kmatzen/millennium/HANDOFF.md

# Millennium continuation handoff

The authoritative objective is to address every unchecked item in
[`TODO.md`](TODO.md). Do not treat a passing QEMU run as proof of a physical
Zero 2 W, radio, USB, audio, power, or first-time-user requirement.

## Current repository state

- Working branch: `main`.
- Current candidate `27b69be9a35c361adab7c90882842096d9612346`
  supersedes and rejects `7033d94` and `c409237`. Physical boot of `c409237`
  proved owner Wi-Fi association, setup-AP shutdown, and the outbound
  maintenance tunnel, but both application and OS update checks failed at
  systemd namespace setup because their persistent state roots were absent.
  `27b69be` provisions every production `ReadWritePaths` state root (`ota`,
  `os-ota`, `hil`, `backup`, and `physical-tests`) with required ownership and
  modes. Exact-image acceptance checks and writes every root through
  `ProtectSystem=strict` on both system slots. The full QEMU lab, host suite,
  contracts suite, and formal release gate passed on `anima`. The canonical
  package is signed with `release-2026-08` and independently verified on
  macOS, `anima`, and external `UEBuild`; dedicated-media write/readback and
  physical boot remain open. Evidence is in
  `hardware/as-built/phone-001/evidence/zero2w-recovery-seeded-artifact-27b69be-2026-09-11.json`.
- Candidate `4a15bf63c9d4a44532d015f8212d44a2a987e7c1` was built and
  factory-seeded on `anima`. Its exact seeded image passed the commit-bound
  automated release gate. Its canonical recovery manifest is signed with the
  verified active `release-2026-08` key and independently verified on macOS
  and `anima`. The non-overwriting external `UEBuild` copy also passed all four
  hashes, signature, public-key identity, and full expansion checks without
  using laptop internal storage. On 2026-09-09 the dedicated 63.9 GB USB card
  was signature-verified, written, flushed, and read back over the complete
  image length; its readback SHA-256 matched the signed expanded digest. The
  card was then safely ejected. Evidence is in
  `hardware/as-built/phone-001/evidence/recovery-media-phone001-4a15bf6.json`.
  It is rejected: physical boot showed `daemon.service` failing with
  `203/EXEC` because `/opt/millennium` was `root:root 0750` and the
  unprivileged service user could not traverse it. The
  expanded image is
  `/data2/millennium-build-4a15bf6/phone001-4a15bf6.img`, is
  15,636,365,312 bytes, and has SHA-256
  `277044c2d3e2332c07aa7849329ba2589a45136d1eb5110812218c12fd75f8ef`.
- Corrected image-layer source `1f637722b3d2403308392e40912da2c5831ec5e7`
  normalizes `/opt` and `/opt/millennium` to `root:root 0755`. Test-harness
  source `ff277828c6bf0b3f7bb6b6a95294e836c53e1c0a` eliminates the echoed-marker
  false positive, tests both system slots, executes the production daemon as
  user `millennium`, and rejects `203/EXEC`. The unchanged application payload
  remains from `4a15bf6`. The corrected 15,636,365,312-byte factory image has
  SHA-256 `aa1b2b0b1d5b312709666db22d6246ae0cfd921ba13cce595a59893ed5142e71`.
  A fresh full QEMU lab passed at `2026-09-09T18:20:21Z`; its result SHA-256 is
  `09d8e2ab11695b2f09bdc0bcbae4d4a2aa7e64bc764649285ded6e8d7cf552ee`.
  The canonical recovery package is signed and independently verified on
  macOS and `anima`. A direct, non-overwriting external `UEBuild` copy passed
  all four stored hashes, signature, public-key identity, and the complete
  expanded stream without using laptop internal storage. On 2026-09-10 the
  OS-identified 63.9 GB removable card was written, flushed, completely read
  back, matched the signed expanded SHA-256, and safely ejected. Physical boot
  remains open.
  Evidence is in `hardware/as-built/phone-001/evidence/zero2w-recovery-seeded-artifact-1f63772-2026-09-09.json`.
- The prior production images were built from earlier sources. The
  physically booted `6f50d12`, `c9b01fb`, `d895b35`, and `98e018a` candidates are
  rejected. Physical
  `d895b35` tracing proved the Zero 2 W AP-to-station transition can exceed
  seven seconds, while its helper stopped retrying after four; `b496081`
  extends the bounded retry window and adds the measured-delay regression.
  The `98e018a` boot then exposed an activated-but-not-beaconing setup AP;
  `6dad08e` forces every setup/recovery start through a down/up cycle.
- The `98e018a` factory-seeded candidate is signed and verified. Its compressed
  SHA-256 is `62dff50153247725982648819caa0d1f2cd9d755a679264dadb89964c46df795`;
  its expanded and readback SHA-256 is
  `d02b6ee091542cc0ee7158a3e46aa4f3078738b545e275933d91b14bd4a759a6`.
  Media evidence is in
  `hardware/as-built/phone-001/evidence/recovery-media-phone001-98e018a.json`.
- The rejected `d895b35` factory-seeded candidate is signed, independently verified,
  retained on `anima`, copied directly to external `UEBuild`, written to the
  dedicated 63.9 GB recovery card, and fully read back. Its compressed SHA-256
  is `d0bba17c794f1980e23a933fea716552f74d2bee8fd103906d1e84235d9c80e7`;
  its expanded and readback SHA-256 is
  `01273e50f108d50f361672b58b9ccfac98340685bede42a61c895dd91b6c23b9`.
- The latest commit-bound QEMU software lab passed at
  `2026-09-09T18:20:21Z`, including both system slots of the exact corrected
  `1f63772` factory image, production-daemon execution as its service user,
  external captive-portal client, OTA origin and failures, maintenance tunnel,
  virtual MCU/peripheral faults, A/B recovery, experiences, and abrupt power.
  Exact evidence is in
  `/data2/millennium-build-1f63772/repo/tools/qemu/state/artifacts/full-20260909T171854Z/`
  on `anima`.
- CI run `34381944039` passed all jobs for test-harness commit `ff27782`; CI run
  `34377452413` passed image-layer commit `1f63772`. The full-test result
  explicitly records that no physical hardware claim was made.
- Latest completed downloadable-experience commits:
  - `f53b54c` — generated package/catalog schemas and compatibility metadata;
  - `d35f4fa` — deterministic schema-2 packages, bounded extraction, exact file
    inventory, compatibility checks, and persistent package anti-rollback;
  - `40c7df7` — deterministic signed catalog creation and local rollout,
    hold/group/withdrawal/denylist eligibility.
- QEMU hardening is in `13b62a6`; the prior full exact-image evidence was
  generated from the production image and passed all 18 artifact hashes.
- The final local software audit on 2026-09-07 passed 151 host unit tests, 6
  web-authorization tests, 2 owner-boundary tests, 50 content/story/security
  tests, 68 tools tests, every simulator scenario, 16 OTA tests, generated
  schema/version checks, and `git diff --check`.
- The 2026-09-07 plugged-media rerun exposed and fixed two QEMU portability
  defects: initramfs `/run` discarded the exact-image udev aliases before
  systemd consumed them, and Linux does not guarantee the numeric
  `/dev/vportNpM` name. The exact-image harness now injects configuration only
  into its disposable overlay, and the portable lab uses the stable
  `/dev/virtio-ports/millennium.mcu` link. The signed-experience lifecycle also
  establishes the same idle handset state required by the production worker.
- At `2026-09-07T19:13:20Z`, FIDO access to `anima` remained healthy but its
  loopback phone listener `127.0.0.1:22022` was absent; do not infer live-phone
  state until the reverse tunnel returns.

Large QEMU and image artifacts intentionally live on `anima` and external
`UEBuild`, not laptop internal storage. The latest complete QEMU evidence is
`/data2/millennium-build-27b69be/repo/tools/qemu/state/artifacts/full-20260911T004411Z/`
on `anima`; its `full-test-result.json` records a pass with exact production
image userspace tested in both system slots and `physical_hardware_claimed: false`.

## Immediate execution order

1. Write/read back, install, and physically test the signed `27b69be`
   recovery package already verified on external `UEBuild`. Do not redeploy
   rejected `7033d94`, `c409237`, `1f63772`, or
   `4a15bf6`.
   Preserve the rejected `6f50d12`,
   `c9b01fb`, `d895b35`, `98e018a`, and `4a15bf6` media/boot evidence without treating any as
   approval. Both Arduino MCUs are required for the physical health gate;
   phone peripherals may be absent only for explicitly scoped platform
   validation.
2. Publish the immutable release objects and signed stable/beta/device-group
   catalogs with `content/publish_catalog.py` after completing the offline
   content/catalog signing ceremony. FIDO-authenticated access to `anima` is
   working through `/opt/homebrew/bin/ssh`; its operator-writable update root is
   `/home/kmatzen/selfhosted/millennium-updates/www`, bind-mounted read-only into
   the `millennium-updates` nginx container.
   `updates.kmatzen.com` is transport, not trust; signatures remain mandatory.
3. When the assembled phone and operator are available, follow
   [`hardware/as-built/phone-001/NEXT_PHYSICAL_SESSION.md`](hardware/as-built/phone-001/NEXT_PHYSICAL_SESSION.md)
   exactly. That single session is intended to close the remaining P0 physical
   Wi-Fi, A/B OS, power-interruption, recovery-media, external-maintenance,
   as-built, and first-time-caller evidence gaps.

## Required verification

For content/catalog changes, run:

```sh
python3 -m unittest content.tests.test_catalogtool \
  content.tests.test_storytool content.tests.test_content_install \
  content.tests.test_experience_agent content.tests.test_publish_catalog
python3 -m unittest discover -s tools/tests -p 'test_*.py'
python3 tools/generate_experience_schemas.py --check
python3 tools/generate_version_metadata.py --check
git diff --check
```

For full appliance changes, run the retained exact image on `anima`:

```sh
/opt/homebrew/bin/ssh anima \
  'docker exec \
    -e MILLENNIUM_QEMU_EXACT_IMAGE=/image/phone001-1f63772.img \
    -e MILLENNIUM_QEMU_EXACT_KERNEL=/workspace/tools/qemu/state/exact-vmlinuz \
    -e MILLENNIUM_QEMU_EXACT_INITRD=/workspace/tools/qemu/state/exact-initrd \
    millennium-qemu-final-1f63772 tools/qemu/qemu.sh full-test'
```

The custom transport initramfs includes FAT, charset, and nftables modules.
Using the older minimal cloud initramfs creates false boot-partition/firewall
failures and is not an equivalent test.

## Completion discipline

Only check off a TODO item when its scoped evidence exists. In particular,
automated captive-portal probes are not physical iOS/Android/macOS/Windows
tests; QEMU power cuts are not measured Zero 2 W power removal; a tunnel from
the home source network is not a genuinely external maintenance session; and a
scripted story traversal is not a first-time-caller playtest. Preserve failed
evidence and never relabel it as passing.
