kmatzen/millennium/docs/COMPATIBILITY.md

# Generated compatibility metadata

Do not edit this file directly. Run `python3 tools/generate_version_metadata.py`.

| Component | Current value |
| --- | ---: |
| Host and MCU software | `0.4.0` |
| OTA manifest schema | `1` |
| OTA release schema | `1` |
| MCU serial protocol | `2` |
| Story source schema | `1` |
| Story runtime schema | `1` |
| Content manifest schema | `1` |
| Downloadable experience package schema | `2` |
| Downloadable experience catalog schema | `1` |

The host release and both MCU roles must report the same software version.
Protocol or schema changes require an explicit compatibility migration; they
must never be inferred from the marketing version alone.
