kmatzen/millennium/content/AUDIO_LIBRARY.md

# Reusable narrative audio and interaction patterns

The initial reviewed library is embodied by *The House at the End of the Line* 2.1.0. Its clips
are deliberately small, handset-normalized, transcript-backed patterns that a
new story may copy and re-record without inheriting story logic:

| Pattern | Reference clip | Interaction contract |
| --- | --- | --- |
| Invitation | `invitation.wav` | Name the physical action that begins. |
| Choice | `decision.wav` | Speak every valid key and the repeat key. |
| Retry | `decision_retry.wav` | Shorten the prompt without removing choices. |
| Accepted choice | `choose_leave.wav` | Confirm input before any delay. |
| Connection | `dialing.wav` | Explain both online and timeout outcomes. |
| Optional discovery | `coin_secret.wav` | Reward hardware play and state how to return. |
| Interruption | `interrupted.wav` | Reassure the caller and name the resume action. |
| Ending | `leave_result.wav` | State consequence and invite a return. |
| Return recognition | `return_leave.wav` | Acknowledge anonymous persistent state. |
| Coda | `leave_coda.wav` | Pay off the earlier choice without new setup. |
| Incoming callback | physical ring | Respect quiet hours and require an answered handset. |
| Waiting voicemail | `missed.wav` | Preserve a missed return call without nagging. |
| Consequence voicemail | `answer_coda.wav` | Reflect the caller's earlier decision. |

All reference WAVs are mono, 8 kHz, signed 16-bit PCM at -20 LUFS. The source
transcripts and deterministic regeneration command live in
`stories/last_line/regenerate_audio.sh`. New library entries require a
transcript, source/voice and license note, loudness/rate metadata, a VFD-only
fallback, and a scenario that exercises the associated interaction.

These are patterns, not mandatory prose. Authors should preserve the contract
while changing voice, language, and tone to suit the story bible and audience.
