kmatzen/millennium/host/millennium_sdk.h

#ifndef MILLENNIUM_SDK_H
#define MILLENNIUM_SDK_H

#include <stddef.h>
#include <string.h>   /* strlen, for millennium_display_payload_len */
#include <stdint.h>
#include <time.h>
#include "mcu_protocol.h"

#define MCU_COMMAND_QUEUE_CAPACITY 8

/* Forward declarations */
struct millennium_client;
struct millennium_logger;

/* Logger level enumeration */
typedef enum {
    LOGGER_VERBOSE = 0,
    LOGGER_DEBUG,
    LOGGER_INFO,
    LOGGER_WARN,
    LOGGER_ERROR
} logger_level_t;

/* Logger structure */
typedef struct millennium_logger {
    logger_level_t current_level;
} millennium_logger_t;

/* Millennium client structure */
typedef struct millennium_client {
    int display_fd;
    int is_open;
    char *input_buffer;
    size_t input_buffer_size;
    size_t input_buffer_capacity;
    
    /* Event queue - simple linked list implementation */
    struct event_queue_node {
        void *event;
        struct event_queue_node *next;
    } *event_queue_head, *event_queue_tail;
    
    /* Thread handle - using pthread for C89 compatibility */
    void *thread_handle;
    
    char *display_message;
    int display_dirty;
    struct timespec last_update_time;
    void *ua; /* struct ua * */
    
    /* Function pointers for event handling */
    void (*create_and_queue_event_char)(struct millennium_client *client, char event_type, const char *payload);
    void (*create_and_queue_event_ptr)(struct millennium_client *client, void *event);

    /* Serial health tracking */
    struct timespec last_serial_activity;
    struct timespec last_alpha_activity;
    int serial_healthy;
    int reconnect_attempts;
    struct timespec next_reconnect_time;
    char serial_device_path[256];
    int serial_baud_rate;

    /* (#239) Last coin-gate command sent to the validator, replayed after a
     * serial reconnect.  0 until the daemon gates the validator once. */
    uint8_t coin_gate_cmd;

    /* Version-2 framed MCU transport. Critical commands remain pending until
     * the display MCU acknowledges their sequence number. */
    mcu_decoder_t mcu_decoder;
    mcu_replay_guard_t mcu_event_replay;
    uint8_t mcu_tx_sequence;
    uint8_t mcu_protocol_ready;
    struct timespec mcu_protocol_started_at;
    struct timespec mcu_protocol_last_hello_at;
    int serial_replay_pending;
    uint8_t pending_frame[MCU_PROTOCOL_MAX_FRAME];
    size_t pending_frame_length;
    uint8_t pending_sequence;
    int pending_retries;
    struct timespec pending_sent_at;
    uint8_t queued_frames[MCU_COMMAND_QUEUE_CAPACITY][MCU_PROTOCOL_MAX_FRAME];
    size_t queued_frame_lengths[MCU_COMMAND_QUEUE_CAPACITY];
    uint8_t queued_frame_sequences[MCU_COMMAND_QUEUE_CAPACITY];
    size_t command_queue_head;
    size_t command_queue_count;
} millennium_client_t;

/* Function declarations */

/* Logger functions */
logger_level_t millennium_logger_parse_level(const char *level_str);
void millennium_logger_set_level(logger_level_t level);
void millennium_logger_log(logger_level_t level, const char *message);
logger_level_t millennium_logger_get_current_level(void);

/* Millennium client functions */
struct millennium_client *millennium_client_create(void);
void millennium_client_destroy(struct millennium_client *client);
void millennium_client_close(struct millennium_client *client);

/* Event handling */
void millennium_client_create_and_queue_event_char(struct millennium_client *client, char event_type, const char *payload);
void millennium_client_create_and_queue_event_ptr(struct millennium_client *client, void *event);

/* Display and communication */
void millennium_client_set_display(struct millennium_client *client, const char *message);
void millennium_client_write_to_coin_validator(struct millennium_client *client, uint8_t data);
void millennium_client_update(struct millennium_client *client);
void *millennium_client_next_event(struct millennium_client *client);

/* Call functions */
void millennium_client_call(struct millennium_client *client, const char *number);
void millennium_client_answer_call(struct millennium_client *client);
void millennium_client_hangup(struct millennium_client *client);
int millennium_client_send_dtmf(struct millennium_client *client, char key);
void millennium_client_set_ua(struct millennium_client *client, void *ua);

/* Internal functions */
void millennium_client_write_command(struct millennium_client *client, uint8_t command, const uint8_t *data, size_t data_size);
void millennium_client_process_event_buffer(struct millennium_client *client);
char *millennium_client_extract_payload(struct millennium_client *client, char event_type, size_t event_start);
void millennium_client_write_to_display(struct millennium_client *client, const char *message);

/* Serial health and reconnection */
int millennium_client_serial_is_healthy(struct millennium_client *client);
long millennium_client_alpha_idle_seconds(struct millennium_client *client);
void millennium_client_check_serial(struct millennium_client *client);
void millennium_client_serial_activity(struct millennium_client *client);

/* Utility functions */
void list_audio_devices(void);

/* SIP registration status (0=unknown, 1=registered, -1=failed). last_error may be NULL. */
void millennium_sdk_get_sip_status(int *registered, char *last_error, size_t last_error_size);

/* Constants */
#define BAUD_RATE B9600
#define ASYNC_WORKERS 4
#define SERIAL_WATCHDOG_SECONDS 60
#define SERIAL_MAX_BACKOFF_SECONDS 60
#define SERIAL_WATCHDOG_ENABLED 1

/* Largest display payload the protocol-v2 display frame can carry.
 *
 * MUST match `byte buf[100]` in Arduino/sketches/display/display.ino, which
 * rejects any frame declaring more than that (`num_bytes > sizeof(buf)`).
 * The length is also carried in a single byte, so it could never exceed 255
 * regardless.
 *
 * Length and CRC cover exactly this body and the receiver resynchronizes at SOF. */
#define DISPLAY_MAX_PAYLOAD 100

/* Number of bytes millennium_client_write_to_display will actually send for
 * `message`: strlen clamped to DISPLAY_MAX_PAYLOAD, and 0 for NULL.
 *
 * Defined here rather than in millennium_sdk.c so the unit tests can exercise
 * it -- unit_tests does not link millennium_sdk.o, which would pull in the
 * PJSIP symbols that are only available on the Pi.
 *
 * `static inline` (a GNU extension the build already relies on via -std=gnu89)
 * so translation units that never call it do not trip -Wunused-function. */
static inline size_t millennium_display_payload_len(const char *message) {
    size_t len;
    if (!message) return 0;
    len = strlen(message);
    return (len > DISPLAY_MAX_PAYLOAD) ? (size_t)DISPLAY_MAX_PAYLOAD : len;
}

#endif /* MILLENNIUM_SDK_H */
