kmatzen/millennium/host/events.c

#define _POSIX_C_SOURCE 200112L
#include "events.h"
#include "logger.h"
#include <stdlib.h>
#include <string.h>
#include <stdio.h>

size_t event_payload_length(char event_type) {
    switch (event_type) {
    case EVENT_TYPE_KEYPAD:
    case EVENT_TYPE_HOOK:
    case EVENT_TYPE_COIN:
        return 1;
    case EVENT_TYPE_CARD:
        return 16;
    case EVENT_TYPE_EEPROM_ERROR:
        return 3;
    case EVENT_TYPE_DIAG:
        return EVENT_DIAG_PAYLOAD_LEN;
    default:
        return 0;
    }
}

/* Helper function to create a string copy */
static char *strdup_safe(const char *src) {
    size_t len;
    char *dst;
    if (!src) return NULL;
    len = strlen(src);
    dst = malloc(len + 1);
    if (dst) {
        memcpy(dst, src, len);
        dst[len] = '\0';
    }
    return dst;
}

/* Keypad event functions */
static void keypad_event_destroy(void *event) {
    free(event);
}

static const char *keypad_event_get_name(void *event) {
    (void)event;
    return "KeypadEvent";
}

static char *keypad_event_get_repr(void *event) {
    keypad_event_t *ke = (keypad_event_t *)event;
    char *repr = malloc(2);
    if (repr) {
        repr[0] = ke->key;
        repr[1] = '\0';
    }
    return repr;
}

keypad_event_t *keypad_event_create(char key) {
    keypad_event_t *event = malloc(sizeof(keypad_event_t));
    if (!event) return NULL;
    
    event->base.type = EVENT_KEYPAD;
    event->base.destroy = keypad_event_destroy;
    event->base.get_name = keypad_event_get_name;
    event->base.get_repr = keypad_event_get_repr;
    event->key = key;
    
    return event;
}

char keypad_event_get_key(keypad_event_t *event) {
    return event ? event->key : 0;
}

/* Card event functions */
static void card_event_destroy(void *event) {
    card_event_t *card = (card_event_t *)event;
    if (card) memset(card->card_number, 0, sizeof(card->card_number));
    free(event);
}

static const char *card_event_get_name(void *event) {
    (void)event;
    return "CardEvent";
}

static char *card_event_get_repr(void *event) {
    (void)event;
    return strdup_safe("[credential redacted]");
}

card_event_t *card_event_create(const char *card_number) {
    card_event_t *event = malloc(sizeof(card_event_t));
    if (!event) return NULL;
    
    event->base.type = EVENT_CARD;
    event->base.destroy = card_event_destroy;
    event->base.get_name = card_event_get_name;
    event->base.get_repr = card_event_get_repr;
    
    if (card_number) {
        strncpy(event->card_number, card_number, sizeof(event->card_number) - 1);
        event->card_number[sizeof(event->card_number) - 1] = '\0';
    } else {
        event->card_number[0] = '\0';
    }
    
    return event;
}

/* Coin event functions */
static void coin_event_destroy(void *event) {
    free(event);
}

static const char *coin_event_get_name(void *event) {
    (void)event;
    return "CoinEvent";
}

static char *coin_event_get_repr(void *event) {
    return coin_event_get_coin_code((coin_event_t *)event);
}

char *coin_event_get_coin_code(coin_event_t *event) {
    if (!event) return NULL;
    
    switch (event->code) {
    case 0x30:
        return strdup_safe("INVALID_COIN");
    case 0x31:
        return strdup_safe("COIN_1");
    case 0x32:
        return strdup_safe("COIN_2");
    case 0x33:
        return strdup_safe("COIN_3");
    case 0x34:
        return strdup_safe("COIN_4");
    case 0x35:
        return strdup_safe("COIN_5");
    case 0x36:
        return strdup_safe("COIN_6");
    case 0x37:
        return strdup_safe("COIN_7");
    case 0x38:
        return strdup_safe("COIN_8");
    default:
        return strdup_safe("UNKNOWN_COIN");
    }
}

coin_event_t *coin_event_create(uint8_t code) {
    coin_event_t *event = malloc(sizeof(coin_event_t));
    if (!event) return NULL;
    
    event->base.type = EVENT_COIN;
    event->base.destroy = coin_event_destroy;
    event->base.get_name = coin_event_get_name;
    event->base.get_repr = coin_event_get_repr;
    event->code = code;
    
    return event;
}

/* Hook state change event functions */
static void hook_state_change_event_destroy(void *event) {
    free(event);
}

static const char *hook_state_change_event_get_name(void *event) {
    (void)event;
    return "HookStateChangeEvent";
}

static char *hook_state_change_event_get_repr(void *event) {
    hook_state_change_event_t *he = (hook_state_change_event_t *)event;
    return strdup_safe(he->state == 'U' ? "Up" : "Down");
}

hook_state_change_event_t *hook_state_change_event_create(char state) {
    hook_state_change_event_t *event = malloc(sizeof(hook_state_change_event_t));
    if (!event) return NULL;
    
    event->base.type = EVENT_HOOK_STATE_CHANGE;
    event->base.destroy = hook_state_change_event_destroy;
    event->base.get_name = hook_state_change_event_get_name;
    event->base.get_repr = hook_state_change_event_get_repr;
    event->state = state;
    
    return event;
}

char hook_state_change_event_get_direction(hook_state_change_event_t *event) {
    return event ? event->state : 0;
}

/* Coin EEPROM upload start event functions */
static void coin_eeprom_upload_start_destroy(void *event) {
    free(event);
}

static const char *coin_eeprom_upload_start_get_name(void *event) {
    (void)event;
    return "CoinEepromUploadStart";
}

static char *coin_eeprom_upload_start_get_repr(void *event) {
    (void)event;
    return strdup_safe("");
}

coin_eeprom_upload_start_t *coin_eeprom_upload_start_create(void) {
    coin_eeprom_upload_start_t *event = malloc(sizeof(coin_eeprom_upload_start_t));
    if (!event) return NULL;
    
    event->base.type = EVENT_COIN_EEPROM_UPLOAD_START;
    event->base.destroy = coin_eeprom_upload_start_destroy;
    event->base.get_name = coin_eeprom_upload_start_get_name;
    event->base.get_repr = coin_eeprom_upload_start_get_repr;
    
    return event;
}

/* Coin EEPROM upload end event functions */
static void coin_eeprom_upload_end_destroy(void *event) {
    free(event);
}

static const char *coin_eeprom_upload_end_get_name(void *event) {
    (void)event;
    return "CoinEepromUploadEnd";
}

static char *coin_eeprom_upload_end_get_repr(void *event) {
    (void)event;
    return strdup_safe("");
}

coin_eeprom_upload_end_t *coin_eeprom_upload_end_create(void) {
    coin_eeprom_upload_end_t *event = malloc(sizeof(coin_eeprom_upload_end_t));
    if (!event) return NULL;
    
    event->base.type = EVENT_COIN_EEPROM_UPLOAD_END;
    event->base.destroy = coin_eeprom_upload_end_destroy;
    event->base.get_name = coin_eeprom_upload_end_get_name;
    event->base.get_repr = coin_eeprom_upload_end_get_repr;
    
    return event;
}

/* Coin EEPROM validation start event functions */
static void coin_eeprom_validation_start_destroy(void *event) {
    free(event);
}

static const char *coin_eeprom_validation_start_get_name(void *event) {
    (void)event;
    return "CoinEepromValidationStart";
}

static char *coin_eeprom_validation_start_get_repr(void *event) {
    (void)event;
    return strdup_safe("");
}

coin_eeprom_validation_start_t *coin_eeprom_validation_start_create(void) {
    coin_eeprom_validation_start_t *event = malloc(sizeof(coin_eeprom_validation_start_t));
    if (!event) return NULL;
    
    event->base.type = EVENT_COIN_EEPROM_VALIDATION_START;
    event->base.destroy = coin_eeprom_validation_start_destroy;
    event->base.get_name = coin_eeprom_validation_start_get_name;
    event->base.get_repr = coin_eeprom_validation_start_get_repr;
    
    return event;
}

/* Coin EEPROM validation end event functions */
static void coin_eeprom_validation_end_destroy(void *event) {
    free(event);
}

static const char *coin_eeprom_validation_end_get_name(void *event) {
    (void)event;
    return "CoinEepromValidationEnd";
}

static char *coin_eeprom_validation_end_get_repr(void *event) {
    (void)event;
    return strdup_safe("");
}

coin_eeprom_validation_end_t *coin_eeprom_validation_end_create(void) {
    coin_eeprom_validation_end_t *event = malloc(sizeof(coin_eeprom_validation_end_t));
    if (!event) return NULL;
    
    event->base.type = EVENT_COIN_EEPROM_VALIDATION_END;
    event->base.destroy = coin_eeprom_validation_end_destroy;
    event->base.get_name = coin_eeprom_validation_end_get_name;
    event->base.get_repr = coin_eeprom_validation_end_get_repr;
    
    return event;
}

/* Coin EEPROM validation error event functions */
static void coin_eeprom_validation_error_destroy(void *event) {
    free(event);
}

static const char *coin_eeprom_validation_error_get_name(void *event) {
    (void)event;
    return "CoinEepromValidationError";
}

static char *coin_eeprom_validation_error_get_repr(void *event) {
    coin_eeprom_validation_error_t *ee = (coin_eeprom_validation_error_t *)event;
    char *repr = malloc(64);
    if (repr) {
        snprintf(repr, 64, "Addr: %d, Expected: %d, Actual: %d", 
                ee->addr, ee->expected, ee->actual);
    }
    return repr;
}

coin_eeprom_validation_error_t *coin_eeprom_validation_error_create(uint8_t addr, uint8_t expected, uint8_t actual) {
    coin_eeprom_validation_error_t *event = malloc(sizeof(coin_eeprom_validation_error_t));
    if (!event) return NULL;
    
    event->base.type = EVENT_COIN_EEPROM_VALIDATION_ERROR;
    event->base.destroy = coin_eeprom_validation_error_destroy;
    event->base.get_name = coin_eeprom_validation_error_get_name;
    event->base.get_repr = coin_eeprom_validation_error_get_repr;
    event->addr = addr;
    event->expected = expected;
    event->actual = actual;
    
    return event;
}

/* Call state event functions */
static void call_state_event_destroy(void *event) {
    free(event);
}

static const char *call_state_event_get_name(void *event) {
    (void)event;
    return "CallStateEvent";
}

static char *call_state_event_get_repr(void *event) {
    call_state_event_t *ce = (call_state_event_t *)event;
    return strdup_safe(ce->state);
}

call_state_event_t *call_state_event_create(const char *state, struct call *call, call_state_t state_value) {
    call_state_event_t *event = malloc(sizeof(call_state_event_t));
    if (!event) return NULL;
    
    event->base.type = EVENT_CALL_STATE;
    event->base.destroy = call_state_event_destroy;
    event->base.get_name = call_state_event_get_name;
    event->base.get_repr = call_state_event_get_repr;
    
    if (state) {
        strncpy(event->state, state, sizeof(event->state) - 1);
        event->state[sizeof(event->state) - 1] = '\0';
    } else {
        event->state[0] = '\0';
    }
    
    event->call = call;
    event->state_value = state_value;
    
    return event;
}

call_state_t call_state_event_get_state(call_state_event_t *event) {
    return event ? event->state_value : EVENT_CALL_STATE_INVALID;
}

struct call *call_state_event_get_call(call_state_event_t *event) {
    return event ? event->call : NULL;
}

/* Generic event functions */
void event_destroy(event_t *event) {
    if (event && event->destroy) {
        event->destroy(event);
    }
}

const char *event_get_name(event_t *event) {
    if (event && event->get_name) {
        return event->get_name(event);
    }
    return "UnknownEvent";
}

char *event_get_repr(event_t *event) {
    if (event && event->get_repr) {
        return event->get_repr(event);
    }
    return strdup_safe("Unknown");
}

/* (#230) Decode an Arduino diagnostic payload: source letter + 3 ASCII digits.
 *
 * Strict about the digits on purpose. This rides the same serial stream as
 * keypresses and coins, and process_event_buffer() consumes a fixed width, so
 * a malformed payload means the stream is already misaligned -- inventing a
 * number from it would turn a parsing bug into a bogus metric. */
int event_diag_parse(const char *payload, const char **source, long *count) {
    long n;
    int i;

    if (!payload || !source || !count) return 0;
    if (strlen(payload) < EVENT_DIAG_PAYLOAD_LEN) return 0;

    if (payload[0] == 'A') {
        *source = "alpha";
    } else if (payload[0] == 'B') {
        *source = "beta";
    } else {
        return 0;
    }

    n = 0;
    for (i = 1; i < EVENT_DIAG_PAYLOAD_LEN; i++) {
        if (payload[i] < '0' || payload[i] > '9') return 0;
        n = n * 10 + (payload[i] - '0');
    }

    *count = n;
    return 1;
}

int event_i2c_error_parse(const char *payload, int *code, long *count) {
    if (!payload || !code || !count) return 0;
    if (strlen(payload) < EVENT_DIAG_PAYLOAD_LEN || payload[0] != 'I') return 0;
    if (payload[1] < '1' || payload[1] > '4' ||
        payload[2] < '0' || payload[2] > '9' ||
        payload[3] < '0' || payload[3] > '9') return 0;
    *code = payload[1] - '0';
    *count = (payload[2] - '0') * 10 + (payload[3] - '0');
    return 1;
}

/* Decode reset diagnostics: K/D (keypad/display) plus decimal MCUSR bitmask. */
int event_reset_parse(const char *payload, const char **role, long *cause) {
    long n;
    int i;

    if (!payload || !role || !cause) return 0;
    if (strlen(payload) < EVENT_DIAG_PAYLOAD_LEN) return 0;
    if (payload[0] == 'K') {
        *role = "keypad";
    } else if (payload[0] == 'D') {
        *role = "display";
    } else {
        return 0;
    }
    n = 0;
    for (i = 1; i < EVENT_DIAG_PAYLOAD_LEN; i++) {
        if (payload[i] < '0' || payload[i] > '9') return 0;
        n = n * 10 + (payload[i] - '0');
    }
    if (n < 0 || n > 255) return 0;
    *cause = n;
    return 1;
}
