kmatzen/millennium/host/web_server.c

#define _POSIX_C_SOURCE 200112L
#include "web_server.h"
#include "config.h"
#include "logger.h"
#include "metrics.h"
#include "health_monitor.h"
#include "plugins.h"
#include "display_manager.h"
#include "websocket.h"
#include "version.h"
#include "updater.h"
#include "experience_owner.h"

#include <sys/socket.h>
#include <sys/select.h>
#include <sys/time.h>
#include <netinet/in.h>
#include <arpa/inet.h>
#include <unistd.h>
#include <fcntl.h>
#include <string.h>
#include <stdio.h>
#include <stdlib.h>
#include <errno.h>
#include <time.h>
#include <ctype.h>
#include <pthread.h>
#include <unistd.h>

/* External references to daemon state (will be set by daemon) */
extern void* daemon_state;
extern void* client;

/* Daemon state structure is now defined in web_server.h */

/* Function declarations for daemon integration */
struct daemon_state_info get_daemon_state_info(void);
time_t get_daemon_start_time(void);
int send_control_command(const char* action);

/* Thread function for web server */
void* web_server_thread_func(void* arg);
static void* web_server_worker_func(void* arg);

/* String utility functions */
void web_server_strcpy_safe(char* dest, const char* src, size_t dest_size) {
    size_t i;
    if (!dest || !src || dest_size == 0) return;

    for (i = 0; i < dest_size - 1 && src[i] != '\0'; i++) {
        dest[i] = src[i];
    }
    dest[i] = '\0';
}

void web_server_strcat_safe(char* dest, const char* src, size_t dest_size) {
    size_t dest_len;
    size_t i;
    if (!dest || !src || dest_size == 0) return;

    dest_len = web_server_strlen_safe(dest);
    if (dest_len >= dest_size - 1) return;

    for (i = 0; i < dest_size - dest_len - 1 && src[i] != '\0'; i++) {
        dest[dest_len + i] = src[i];
    }
    dest[dest_len + i] = '\0';
}

int web_server_strcmp_safe(const char* str1, const char* str2) {
    if (!str1 && !str2) return 0;
    if (!str1) return -1;
    if (!str2) return 1;
    return strcmp(str1, str2);
}

char* web_server_strstr_safe(const char* haystack, const char* needle) {
    if (!haystack || !needle) return NULL;
    return strstr(haystack, needle);
}

size_t web_server_strlen_safe(const char* str) {
    if (!str) return 0;
    return strlen(str);
}

/* JSON escape: escape " and \ for safe embedding in JSON string values */
static void web_server_json_escape(const char* src, char* dest, size_t dest_size) {
    const char* s;
    char* d;
    if (!src || !dest || dest_size == 0) return;
    for (s = src, d = dest; *s && (size_t)(d - dest) < dest_size - 2; s++) {
        if (*s == '"' || *s == '\\') *d++ = '\\';
        *d++ = *s;
    }
    *d = '\0';
}

/* Memory management */
void* web_server_malloc(size_t size) {
    return malloc(size);
}

void web_server_free(void* ptr) {
    if (ptr) free(ptr);
}

/* Case-insensitive string comparison for C89 compatibility */
int web_server_strcasecmp(const char* s1, const char* s2) {
    if (!s1 && !s2) return 0;
    if (!s1) return -1;
    if (!s2) return 1;
    
    while (*s1 && *s2) {
        char c1 = tolower(*s1);
        char c2 = tolower(*s2);
        if (c1 != c2) {
            return c1 - c2;
        }
        s1++;
        s2++;
    }
    return tolower(*s1) - tolower(*s2);
}

/* WebServer creation and destruction */
struct web_server* web_server_create(int port) {
    int i;
    struct web_server* server = (struct web_server*)web_server_malloc(sizeof(struct web_server));
    if (!server) return NULL;

    memset(server, 0, sizeof(struct web_server));
    server->port = port;
    web_server_strcpy_safe(server->bind_address, "127.0.0.1",
                           sizeof(server->bind_address));
    server->running = 0;
    server->should_stop = 0;
    server->paused = 0;
    server->server_fd = -1;
    server->route_count = 0;
    server->static_count = 0;
    server->websocket_count = 0;
    server->rate_limit_count = 0;
    server->worker_count = 0;

    if (conn_queue_init(&server->conn_queue, WEB_SERVER_QUEUE_DEPTH) != 0) {
        logger_error_with_category("WebServer", "Failed to init connection queue");
        web_server_free(server);
        return NULL;
    }
    if (pthread_mutex_init(&server->state_mutex, NULL) != 0) {
        logger_error_with_category("WebServer", "Failed to init state mutex");
        conn_queue_destroy(&server->conn_queue);
        web_server_free(server);
        return NULL;
    }

    /* Initialize static route flags */
    for (i = 0; i < 16; i++) {
        server->static_is_file[i] = 0;
    }

    return server;
}

void web_server_set_bind_address(struct web_server* server, const char* address) {
    if (!server || !address || !address[0]) return;
    web_server_strcpy_safe(server->bind_address, address,
                           sizeof(server->bind_address));
}

void web_server_set_admin_token(struct web_server* server, const char* token) {
    if (!server) return;
    web_server_strcpy_safe(server->admin_token, token ? token : "",
                           sizeof(server->admin_token));
}

void web_server_set_allowed_origin(struct web_server* server, const char* origin) {
    if (!server) return;
    web_server_strcpy_safe(server->allowed_origin, origin ? origin : "",
                           sizeof(server->allowed_origin));
}

void web_server_destroy(struct web_server* server) {
    if (!server) return;
    
    web_server_stop(server);
    conn_queue_destroy(&server->conn_queue);
    pthread_mutex_destroy(&server->state_mutex);
    web_server_free(server);
}

/* WebServer control functions */
void web_server_start(struct web_server* server) {
    if (!server || server->running) return;
    
    server->should_stop = 0;
    server->running = 1;
    
    /* Setup API routes */
    web_server_setup_api_routes(server);
    
    /* Initialize server socket */
    web_server_init_socket(server);
    
    /* Start worker pool before the accept thread so a connection is never
     * enqueued with no one to service it. */
    server->worker_count = 0;
    {
        int w;
        for (w = 0; w < WEB_SERVER_WORKER_COUNT; w++) {
            if (pthread_create(&server->worker_threads[w], NULL,
                               web_server_worker_func, server) != 0) {
                logger_error_with_category("WebServer", "Failed to create worker thread");
                break;
            }
            server->worker_count++;
        }
    }
    if (server->worker_count == 0) {
        logger_error_with_category("WebServer", "No worker threads started; aborting web server");
        server->running = 0;
        if (server->server_fd >= 0) {
            close(server->server_fd);
            server->server_fd = -1;
        }
        return;
    }

    /* Start the accept thread */
    if (pthread_create(&server->server_thread, NULL, web_server_thread_func, server) != 0) {
        logger_error_with_category("WebServer", "Failed to create server thread");
        /* Unwind the workers we just started. */
        conn_queue_close(&server->conn_queue);
        {
            int w;
            for (w = 0; w < server->worker_count; w++) {
                pthread_join(server->worker_threads[w], NULL);
            }
        }
        server->worker_count = 0;
        server->running = 0;
        if (server->server_fd >= 0) {
            close(server->server_fd);
            server->server_fd = -1;
        }
    }
}

void web_server_stop(struct web_server* server) {
    if (!server || !server->running) return;
    
    server->should_stop = 1;

    /* Stop accepting first: the accept thread sees should_stop and returns. */
    pthread_join(server->server_thread, NULL);

    /* Then drain the worker pool: close the queue so blocked workers wake and
     * exit once any remaining queued connections are serviced. */
    conn_queue_close(&server->conn_queue);
    {
        int w;
        for (w = 0; w < server->worker_count; w++) {
            pthread_join(server->worker_threads[w], NULL);
        }
    }
    server->worker_count = 0;

    server->running = 0;

    if (server->server_fd >= 0) {
        close(server->server_fd);
        server->server_fd = -1;
    }

    logger_info_with_category("WebServer", "Web server stopped");
}

void web_server_pause(struct web_server* server) {
    if (!server) return;
    server->paused = 1;
    logger_info_with_category("WebServer", "Web server paused for audio protection");
}

void web_server_resume(struct web_server* server) {
    if (!server) return;
    server->paused = 0;
    logger_info_with_category("WebServer", "Web server resumed");
}

int web_server_is_running(const struct web_server* server) {
    return server ? server->running : 0;
}

int web_server_is_paused(const struct web_server* server) {
    return server ? server->paused : 0;
}

void web_server_get_conn_stats(struct web_server* server, struct conn_queue_stats* out) {
    if (!out) return;
    /* conn_queue_get_stats zeroes the output when handed a NULL queue. */
    conn_queue_get_stats(server ? &server->conn_queue : NULL, out);
}

void web_server_set_port(struct web_server* server, int port) {
    if (!server) return;
    
    if (server->running) {
        logger_warn_with_category("WebServer", "Cannot change port while server is running");
        return;
    }
    server->port = port;
}

int web_server_get_port(const struct web_server* server) {
    return server ? server->port : 0;
}

/* Route management */
void web_server_add_route(struct web_server* server, const char* method, const char* path, route_handler_t handler) {
    int idx;
    if (!server || !method || !path || !handler) return;
    if (server->route_count >= 32) return; /* Max routes reached */

    idx = server->route_count;
    web_server_strcpy_safe(server->route_methods[idx], method, sizeof(server->route_methods[idx]));
    web_server_strcpy_safe(server->route_paths[idx], path, sizeof(server->route_paths[idx]));
    server->route_handlers[idx] = handler;
    server->route_count++;
}

void web_server_add_static_route(struct web_server* server, const char* path, const char* content, const char* content_type) {
    int idx;
    if (!server || !path || !content || !content_type) return;
    if (server->static_count >= 16) return; /* Max static routes reached */

    idx = server->static_count;
    web_server_strcpy_safe(server->static_paths[idx], path, sizeof(server->static_paths[idx]));
    web_server_strcpy_safe(server->static_contents[idx], content, sizeof(server->static_contents[idx]));
    web_server_strcpy_safe(server->static_content_types[idx], content_type, sizeof(server->static_content_types[idx]));
    server->static_is_file[idx] = 0;  /* Using content, not file */
    server->static_count++;
}

void web_server_add_file_route(struct web_server* server, const char* path, const char* file_path, const char* content_type) {
    int idx;
    if (!server || !path || !file_path || !content_type) return;
    if (server->static_count >= 16) return; /* Max static routes reached */

    idx = server->static_count;
    web_server_strcpy_safe(server->static_paths[idx], path, sizeof(server->static_paths[idx]));
    web_server_strcpy_safe(server->static_file_paths[idx], file_path, sizeof(server->static_file_paths[idx]));
    web_server_strcpy_safe(server->static_content_types[idx], content_type, sizeof(server->static_content_types[idx]));
    server->static_is_file[idx] = 1;  /* Using file path */
    server->static_count++;
}

/* HTTP parsing functions */
struct http_request web_server_parse_request(const char* raw_request) {
    struct http_request request;
    const char* line_start;
    const char* line_end;
    char request_line[512];
    size_t line_len;
    char* cr_pos;
    char* query_pos;
    const char* header_start;
    memset(&request, 0, sizeof(request));

    if (!raw_request) return request;

    /* Parse request line */
    line_start = raw_request;
    line_end = strchr(line_start, '\n');
    if (!line_end) return request;

    /* Extract method and path */
    line_len = line_end - line_start;
    if (line_len >= sizeof(request_line)) line_len = sizeof(request_line) - 1;

    memcpy(request_line, line_start, line_len);
    request_line[line_len] = '\0';

    /* Remove \r if present */
    cr_pos = strchr(request_line, '\r');
    if (cr_pos) *cr_pos = '\0';

    /* Parse method and path */
    if (sscanf(request_line, "%15s %255s", request.method, request.path) != 2) {
        return request;
    }

    /* Remove query parameters from path */
    query_pos = strchr(request.path, '?');
    if (query_pos) {
        *query_pos = '\0';
        web_server_parse_query_string(query_pos + 1, &request);
    }

    /* Parse headers */
    header_start = line_end + 1;
    while (header_start && *header_start != '\0') {
        const char* header_end;
        char header_line[512];
        size_t header_len;
        char* cr_pos;
        char* colon_pos;
        header_end = strchr(header_start, '\n');
        if (!header_end) break;

        /* Check for end of headers (empty line) */
        if (header_end == header_start + 1) {
            break;
        }

        header_len = header_end - header_start;
        if (header_len >= sizeof(header_line)) header_len = sizeof(header_line) - 1;

        memcpy(header_line, header_start, header_len);
        header_line[header_len] = '\0';

        /* Remove \r if present */
        cr_pos = strchr(header_line, '\r');
        if (cr_pos) *cr_pos = '\0';

        /* Parse header key:value */
        colon_pos = strchr(header_line, ':');
        if (colon_pos && request.header_count < 32) {
            char* key;
            char* value;
            char* key_end;
            char* value_end;
            *colon_pos = '\0';
            key = header_line;
            value = colon_pos + 1;

            /* Trim whitespace */
            while (*key == ' ' || *key == '\t') key++;
            while (*value == ' ' || *value == '\t') value++;

            key_end = key + strlen(key) - 1;
            while (key_end > key && (*key_end == ' ' || *key_end == '\t' || *key_end == '\r')) {
                *key_end = '\0';
                key_end--;
            }

            value_end = value + strlen(value) - 1;
            while (value_end > value && (*value_end == ' ' || *value_end == '\t' || *value_end == '\r')) {
                *value_end = '\0';
                value_end--;
            }
            
            web_server_strcpy_safe(request.header_keys[request.header_count], key, sizeof(request.header_keys[request.header_count]));
            web_server_strcpy_safe(request.header_values[request.header_count], value, sizeof(request.header_values[request.header_count]));
            request.header_count++;
        }
        
        header_start = header_end + 1;
    }
    
    /* Parse body */
    if (header_start && *header_start != '\0') {
        size_t body_len = strlen(header_start);
        if (body_len >= sizeof(request.body)) body_len = sizeof(request.body) - 1;
        memcpy(request.body, header_start, body_len);
        request.body[body_len] = '\0';
    }
    
    return request;
}

void web_server_parse_query_string(const char* query, struct http_request* request) {
    const char* start;
    if (!query || !request) return;

    start = query;
    while (*start && request->query_count < 16) {
        const char* end;
        char pair[256];
        size_t pair_len;
        char* eq_pos;
        end = strchr(start, '&');
        if (!end) end = start + strlen(start);

        pair_len = end - start;
        if (pair_len >= sizeof(pair)) pair_len = sizeof(pair) - 1;

        memcpy(pair, start, pair_len);
        pair[pair_len] = '\0';

        eq_pos = strchr(pair, '=');
        if (eq_pos) {
            char* key;
            char* value;
            char decoded_key[64];
            char decoded_value[256];
            *eq_pos = '\0';
            key = pair;
            value = eq_pos + 1;

            /* URL decode */
            web_server_url_decode(key, decoded_key, sizeof(decoded_key));
            web_server_url_decode(value, decoded_value, sizeof(decoded_value));
            
            web_server_strcpy_safe(request->query_keys[request->query_count], decoded_key, sizeof(request->query_keys[request->query_count]));
            web_server_strcpy_safe(request->query_values[request->query_count], decoded_value, sizeof(request->query_values[request->query_count]));
            request->query_count++;
        }
        
        if (*end == '\0') break;
        start = end + 1;
    }
}

char* web_server_url_decode(const char* str, char* result, size_t result_size) {
    size_t i, j;
    if (!str || !result || result_size == 0) return NULL;

    j = 0;
    for (i = 0; str[i] != '\0' && j < result_size - 1; i++) {
        if (str[i] == '%' && i + 2 < strlen(str)) {
            char hex[3] = {str[i+1], str[i+2], '\0'};
            int value = strtol(hex, NULL, 16);
            if (value > 0) {
                result[j++] = (char)value;
                i += 2;
            } else {
                result[j++] = str[i];
            }
        } else if (str[i] == '+') {
            result[j++] = ' ';
        } else {
            result[j++] = str[i];
        }
    }
    result[j] = '\0';
    return result;
}

/* Socket initialization */
void web_server_init_socket(struct web_server* server) {
    int opt;
    struct sockaddr_in address;
    int flags;
    char start_msg[256];
    if (!server) return;

    server->server_fd = socket(AF_INET, SOCK_STREAM, 0);
    if (server->server_fd < 0) {
        logger_error_with_category("WebServer", "Failed to create socket");
        return;
    }

    /* Set socket options for reuse */
    opt = 1;
    setsockopt(server->server_fd, SOL_SOCKET, SO_REUSEADDR, &opt, sizeof(opt));

    address.sin_family = AF_INET;
    if (inet_pton(AF_INET, server->bind_address, &address.sin_addr) != 1) {
        logger_errorf_with_category("WebServer", "Invalid IPv4 bind address: %s",
                                    server->bind_address);
        close(server->server_fd);
        server->server_fd = -1;
        return;
    }
    address.sin_port = htons(server->port);
    
    if (bind(server->server_fd, (struct sockaddr*)&address, sizeof(address)) < 0) {
        char error_msg[256];
        snprintf(error_msg, sizeof(error_msg), "Failed to bind to port %d", server->port);
        logger_error_with_category("WebServer", error_msg);
        close(server->server_fd);
        server->server_fd = -1;
        return;
    }
    
    if (listen(server->server_fd, 10) < 0) {
        logger_error_with_category("WebServer", "Failed to listen on socket");
        close(server->server_fd);
        server->server_fd = -1;
        return;
    }
    
    /* Set socket to non-blocking */
    flags = fcntl(server->server_fd, F_GETFL, 0);
    fcntl(server->server_fd, F_SETFL, flags | O_NONBLOCK);

    snprintf(start_msg, sizeof(start_msg), "Web server started on %s:%d",
             server->bind_address, server->port);
    logger_info_with_category("WebServer", start_msg);
}

/* Short reply sent when the worker queue is saturated, so a flooded server
 * sheds load with a proper 503 instead of silently dropping the connection. */
static void web_server_send_busy(int client_fd) {
    static const char* busy =
        "HTTP/1.1 503 Service Unavailable\r\n"
        "Content-Type: application/json\r\n"
        "Retry-After: 1\r\n"
        "Connection: close\r\n"
        "Content-Length: 23\r\n"
        "\r\n"
        "{\"error\":\"Server busy\"}";
    send(client_fd, busy, strlen(busy), 0);
}

/* Accept thread: accepts connections and hands each off to a worker via the
 * connection queue. Accepting stays cheap so the listen backlog drains quickly
 * even while workers are busy with slow requests (#125). */
void* web_server_thread_func(void* arg) {
    struct web_server* server = (struct web_server*)arg;
    if (!server) return NULL;

    while (!server->should_stop) {
        struct sockaddr_in client_addr;
        socklen_t client_len = sizeof(client_addr);
        struct timeval tv;
        int client_fd = accept(server->server_fd, (struct sockaddr*)&client_addr, &client_len);

        if (client_fd >= 0) {
            if (conn_queue_try_push(&server->conn_queue, client_fd) != 0) {
                /* Backlog full: shed load rather than grow unboundedly. */
                logger_warn_with_category("WebServer",
                    "Connection queue full; rejecting client with 503");
                web_server_send_busy(client_fd);
                close(client_fd);
            }
        } else if (errno != EAGAIN && errno != EWOULDBLOCK) {
            /* Log error if it's not just a non-blocking accept */
            char error_msg[256];
            snprintf(error_msg, sizeof(error_msg), "Accept failed with error: %d", errno);
            logger_error_with_category("WebServer", error_msg);
        }

        /* Small sleep to prevent busy waiting */
        /* Use select() for C89-compatible microsecond sleep */
        tv.tv_sec = 0;
        tv.tv_usec = 1000; /* 1ms */
        select(0, NULL, NULL, NULL, &tv);
    }

    return NULL;
}

/* Worker thread: services one accepted connection at a time, pulled from the
 * shared queue. Multiple workers run concurrently, so a slow or expensive
 * request only occupies its own worker instead of blocking every client. */
static void* web_server_worker_func(void* arg) {
    struct web_server* server = (struct web_server*)arg;
    if (!server) return NULL;

    for (;;) {
        int client_fd = conn_queue_pop(&server->conn_queue);
        if (client_fd < 0) {
            break; /* Queue closed and drained: shut the worker down. */
        }
        web_server_handle_client(server, client_fd);
    }

    return NULL;
}

/* Case-insensitively scan request text line-by-line for the Content-Length
 * header and return its value, or -1 if absent/malformed. Scanning per-line
 * (not a raw substring search) avoids matching the token inside a body. */
static long web_server_parse_content_length(const char* buf) {
    const char* p = buf;
    while (p && *p) {
        const char* h = p;
        const char* n = "content-length:";
        while (*n && *h && (char)tolower((unsigned char)*h) == *n) {
            h++;
            n++;
        }
        if (*n == '\0') {
            while (*h == ' ' || *h == '\t') h++;
            return strtol(h, NULL, 10);
        }
        p = strchr(p, '\n');
        if (p) p++;
    }
    return -1;
}

void web_server_handle_client(struct web_server* server, int client_fd) {
    char buffer[4096];
    ssize_t bytes_read;
    size_t total = 0;
    char* header_end = NULL;
    long content_length = -1;
    struct timeval tv;
    if (!server) {
        close(client_fd);
        return;
    }

    /* A request's headers and body can arrive in separate TCP segments, so a
     * single read() often returns only the headers with the body still in
     * flight. That left POST bodies empty — the cause of /api/control
     * intermittently reporting "Unknown action: unknown". Read until the whole
     * body (per Content-Length) has arrived. A receive timeout keeps a slow or
     * stalled client from hanging the single-threaded accept loop. */
    tv.tv_sec = 2;
    tv.tv_usec = 0;
    setsockopt(client_fd, SOL_SOCKET, SO_RCVTIMEO, &tv, sizeof(tv));

    memset(buffer, 0, sizeof(buffer));
    while (total < sizeof(buffer) - 1) {
        bytes_read = read(client_fd, buffer + total, sizeof(buffer) - 1 - total);
        if (bytes_read <= 0) {
            break;   /* EOF, error, or receive timeout */
        }
        total += (size_t)bytes_read;
        buffer[total] = '\0';

        if (!header_end) {
            header_end = strstr(buffer, "\r\n\r\n");
            if (header_end) {
                header_end += 4;
            } else {
                char* alt = strstr(buffer, "\n\n");
                if (alt) header_end = alt + 2;
            }
            if (header_end) {
                content_length = web_server_parse_content_length(buffer);
            }
        }
        if (header_end) {
            /* No body expected (e.g. GET): headers alone are enough. */
            if (content_length < 0) {
                break;
            }
            /* Stop once the declared body length has been received. */
            if ((size_t)(buffer + total - header_end) >= (size_t)content_length) {
                break;
            }
        }
    }

    if (total > 0) {
        struct http_request parsed_request = web_server_parse_request(buffer);
        struct http_response response;

        /* Get client IP for rate limiting */
        struct sockaddr_in client_addr;
        socklen_t client_len = sizeof(client_addr);
        /* inet_ntop (not inet_ntoa) so concurrent workers don't race on a
         * shared static buffer. */
        if (getpeername(client_fd, (struct sockaddr*)&client_addr, &client_len) == 0 &&
            inet_ntop(AF_INET, &client_addr.sin_addr, parsed_request.client_ip,
                      sizeof(parsed_request.client_ip)) != NULL) {
            /* client_ip populated by inet_ntop */
        } else {
            web_server_strcpy_safe(parsed_request.client_ip, "unknown", sizeof(parsed_request.client_ip));
        }

        response = web_server_process_request(server, &parsed_request);
        
        if (response.status_code == 101) {
            /* WebSocket upgrade — send handshake then keep fd open */
            char* response_str = web_server_serialize_response(&response);
            if (response_str) {
                send(client_fd, response_str, strlen(response_str), 0);
                web_server_free(response_str);
            }
            pthread_mutex_lock(&server->state_mutex);
            if (server->websocket_count < 32) {
                int total;
                server->websocket_connections[server->websocket_count++] = client_fd;
                total = server->websocket_count;
                pthread_mutex_unlock(&server->state_mutex);
                logger_infof_with_category("WebServer",
                    "WebSocket client connected (fd=%d, total=%d)",
                    client_fd, total);
            } else {
                pthread_mutex_unlock(&server->state_mutex);
                logger_warn_with_category("WebServer", "Max WebSocket connections reached");
                close(client_fd);
            }
            return;
        } else if (response.is_streaming) {
            web_server_send_streaming_response(client_fd, &response);
        } else {
            char* response_str = web_server_serialize_response(&response);
            if (response_str) {
                send(client_fd, response_str, strlen(response_str), 0);
                web_server_free(response_str);
            }
        }
    }
    
    close(client_fd);
}

/* Request processing */
struct http_response web_server_process_request(struct web_server* server, const struct http_request* request) {
    struct http_response response;
    int i;
    memset(&response, 0, sizeof(response));
    response.status_code = 200;
    
    if (!server || !request) {
        response.status_code = 500;
        return response;
    }
    
    /* When paused (e.g. during audio), reject requests (#122) */
    if (server->paused) {
        response.status_code = 503;
        web_server_strcpy_safe(response.content_type, "application/json", sizeof(response.content_type));
        web_server_strcpy_safe(response.body, "{\"error\":\"Server paused for audio\"}", sizeof(response.body));
        return response;
    }
    
    /* Apply rate limiting for API endpoints */
    if (strncmp(request->path, "/api/", 5) == 0) {
        if (!web_server_check_rate_limit(server, request->client_ip, request->path)) {
            return web_server_create_rate_limit_response();
        }
    }

    /* State-changing operations are never available anonymously, even on a
     * trusted LAN. The default listener is loopback-only, and this second
     * boundary protects requests arriving through the maintenance tunnel. */
    if ((strcmp(request->method, "POST") == 0 &&
         (strcmp(request->path, "/api/control") == 0 ||
          strcmp(request->path, "/api/update") == 0 ||
          strcmp(request->path, "/api/experience-control") == 0)) ||
        (strcmp(request->method, "GET") == 0 &&
         strcmp(request->path, "/api/experiences") == 0)) {
        if (!web_server_request_is_admin_authorized(server, request)) {
            response.status_code = 401;
            web_server_strcpy_safe(response.content_type, "application/json",
                                   sizeof(response.content_type));
            web_server_strcpy_safe(response.body,
                "{\"error\":\"Administrative authorization required\"}",
                sizeof(response.body));
            web_server_strcpy_safe(response.header_keys[response.header_count],
                                   "WWW-Authenticate",
                                   sizeof(response.header_keys[response.header_count]));
            web_server_strcpy_safe(response.header_values[response.header_count],
                                   "Bearer realm=\"millennium-admin\"",
                                   sizeof(response.header_values[response.header_count]));
            response.header_count++;
            return response;
        }
    }
    
    /* Check for WebSocket upgrade */
    if (web_server_is_websocket_upgrade(request)) {
        const char *ws_key = NULL;
        char accept_key[64];
        int hi;

        for (hi = 0; hi < request->header_count; hi++) {
            if (web_server_strcasecmp(request->header_keys[hi], "Sec-WebSocket-Key") == 0) {
                ws_key = request->header_values[hi];
                break;
            }
        }

        if (ws_key && ws_compute_accept_key(ws_key, accept_key, sizeof(accept_key)) == 0) {
            response.status_code = 101;
            web_server_strcpy_safe(response.header_keys[response.header_count], "Upgrade", sizeof(response.header_keys[response.header_count]));
            web_server_strcpy_safe(response.header_values[response.header_count], "websocket", sizeof(response.header_values[response.header_count]));
            response.header_count++;
            web_server_strcpy_safe(response.header_keys[response.header_count], "Connection", sizeof(response.header_keys[response.header_count]));
            web_server_strcpy_safe(response.header_values[response.header_count], "Upgrade", sizeof(response.header_values[response.header_count]));
            response.header_count++;
            web_server_strcpy_safe(response.header_keys[response.header_count], "Sec-WebSocket-Accept", sizeof(response.header_keys[response.header_count]));
            web_server_strcpy_safe(response.header_values[response.header_count], accept_key, sizeof(response.header_values[response.header_count]));
            response.header_count++;
        }
        return response;
    }
    
    /* Check static routes first */
    for (i = 0; i < server->static_count; i++) {
        if (strcmp(server->static_paths[i], request->path) == 0) {
            if (server->static_is_file[i]) {
                /* File route - create streaming response */
                FILE* file;
                response.is_streaming = 1;
                web_server_strcpy_safe(response.file_path, server->static_file_paths[i], sizeof(response.file_path));
                web_server_strcpy_safe(response.content_type, server->static_content_types[i], sizeof(response.content_type));

                /* Get file size for Content-Length header */
                file = fopen(response.file_path, "rb");
                if (file) {
                    fseek(file, 0, SEEK_END);
                    response.content_length = ftell(file);
                    fclose(file);
                } else {
                    response.content_length = 0;
                }
            } else {
                /* Content route - use existing behavior */
                response.is_streaming = 0;
                web_server_strcpy_safe(response.body, server->static_contents[i], sizeof(response.body));
                web_server_strcpy_safe(response.content_type, server->static_content_types[i], sizeof(response.content_type));
            }
            return response;
        }
    }
    
    /* Check dynamic routes */
    for (i = 0; i < server->route_count; i++) {
        if (strcmp(server->route_methods[i], request->method) == 0 && 
            strcmp(server->route_paths[i], request->path) == 0) {
            return server->route_handlers[i](request);
        }
    }
    
    /* Default to 404 */
    return web_server_handle_not_found(request);
}

static const char* web_server_get_header(const struct http_request* request,
                                         const char* name) {
    int i;
    if (!request || !name) return NULL;
    for (i = 0; i < request->header_count; i++) {
        if (web_server_strcasecmp(request->header_keys[i], name) == 0)
            return request->header_values[i];
    }
    return NULL;
}

/* Compare secrets without leaking the first mismatching byte through timing. */
static int web_server_secret_equal(const char* a, const char* b) {
    size_t i, alen, blen, maxlen;
    unsigned char diff, av, bv;
    if (!a || !b) return 0;
    alen = strlen(a);
    blen = strlen(b);
    maxlen = alen > blen ? alen : blen;
    diff = (unsigned char)(alen ^ blen);
    for (i = 0; i < maxlen; i++) {
        av = i < alen ? (unsigned char)a[i] : 0;
        bv = i < blen ? (unsigned char)b[i] : 0;
        diff |= (unsigned char)(av ^ bv);
    }
    return diff == 0;
}

int web_server_request_is_admin_authorized(const struct web_server* server,
                                           const struct http_request* request) {
    const char* authorization;
    const char* origin;
    const char* origin_host;
    const char* host;
    const char* supplied;
    if (!server || !request || !server->admin_token[0]) return 0;

    origin = web_server_get_header(request, "Origin");
    if (origin) {
        if (server->allowed_origin[0]) {
            if (strcmp(origin, server->allowed_origin) != 0) return 0;
        } else {
            /* With no explicit public origin, accept only a same-host browser
             * request. Authorization remains mandatory; this check prevents a
             * captured token being driven cross-site. */
            host = web_server_get_header(request, "Host");
            origin_host = strstr(origin, "://");
            origin_host = origin_host ? origin_host + 3 : NULL;
            if (!host || !origin_host || strcmp(origin_host, host) != 0)
                return 0;
        }
    }

    authorization = web_server_get_header(request, "Authorization");
    if (!authorization || strncmp(authorization, "Bearer ", 7) != 0)
        return 0;
    supplied = authorization + 7;
    return web_server_secret_equal(supplied, server->admin_token);
}

int web_server_is_websocket_upgrade(const struct http_request* request) {
    int i;
    int has_upgrade = 0, has_connection = 0;
    if (!request) return 0;

    for (i = 0; i < request->header_count; i++) {
        if (web_server_strcasecmp(request->header_keys[i], "Upgrade") == 0) {
            if (web_server_strcasecmp(request->header_values[i], "websocket") == 0) {
                has_upgrade = 1;
            }
        } else if (web_server_strcasecmp(request->header_keys[i], "Connection") == 0) {
            if (strstr(request->header_values[i], "Upgrade") != NULL) {
                has_connection = 1;
            }
        }
    }
    
    return has_upgrade && has_connection;
}

/* Response serialization */
char* web_server_serialize_response(const struct http_response* response) {
    size_t total_size;
    char* result;
    char* ptr;
    size_t remaining;
    const char* status_text = "OK";
    int written;
    int i;
    size_t body_len;
    if (!response) return NULL;

    /* Calculate total size needed */
    total_size = 1024; /* Base size for status line and headers */
    total_size += strlen(response->body);
    total_size += response->header_count * 128; /* Space for headers */

    result = (char*)web_server_malloc(total_size);
    if (!result) return NULL;

    ptr = result;
    remaining = total_size;

    /* Status line */
    switch (response->status_code) {
        case 200: status_text = "OK"; break;
        case 202: status_text = "Accepted"; break;
        case 400: status_text = "Bad Request"; break;
        case 401: status_text = "Unauthorized"; break;
        case 403: status_text = "Forbidden"; break;
        case 409: status_text = "Conflict"; break;
        case 404: status_text = "Not Found"; break;
        case 500: status_text = "Internal Server Error"; break;
        case 101: status_text = "Switching Protocols"; break;
        case 429: status_text = "Too Many Requests"; break;
        case 503: status_text = "Service Unavailable"; break;
        default: status_text = "Unknown"; break;
    }
    
    written = snprintf(ptr, remaining, "HTTP/1.1 %d %s\r\n", response->status_code, status_text);
    if (written > 0 && (size_t)written < remaining) {
        ptr += written;
        remaining -= written;
    }

    /* Headers */
    for (i = 0; i < response->header_count; i++) {
        written = snprintf(ptr, remaining, "%s: %s\r\n", 
                          response->header_keys[i], response->header_values[i]);
        if (written > 0 && (size_t)written < remaining) {
            ptr += written;
            remaining -= written;
        }
    }
    
    /* Content-Type header if not already set */
    if (strlen(response->content_type) > 0) {
        written = snprintf(ptr, remaining, "Content-Type: %s\r\n", response->content_type);
        if (written > 0 && (size_t)written < remaining) {
            ptr += written;
            remaining -= written;
        }
    }
    
    /* Content-Length header */
    written = snprintf(ptr, remaining, "Content-Length: %lu\r\n", (unsigned long)strlen(response->body));
    if (written > 0 && (size_t)written < remaining) {
        ptr += written;
        remaining -= written;
    }
    
    /* Connection header */
    written = snprintf(ptr, remaining, "Connection: close\r\n\r\n");
    if (written > 0 && (size_t)written < remaining) {
        ptr += written;
        remaining -= written;
    }
    
    /* Body */
    body_len = strlen(response->body);
    if (body_len < remaining) {
        memcpy(ptr, response->body, body_len);
        ptr += body_len;
        *ptr = '\0';
    }
    
    return result;
}

/* API route setup */
void web_server_setup_api_routes(struct web_server* server) {
    if (!server) return;
    
    /* API routes */
    web_server_add_route(server, "GET", "/api/status", web_server_handle_api_status);
    web_server_add_route(server, "GET", "/api/metrics", web_server_handle_api_metrics);
    web_server_add_route(server, "GET", "/api/health", web_server_handle_api_health);
    web_server_add_route(server, "GET", "/api/config", web_server_handle_api_config);
    web_server_add_route(server, "GET", "/api/state", web_server_handle_api_state);
    web_server_add_route(server, "POST", "/api/control", web_server_handle_api_control);
    web_server_add_route(server, "GET", "/api/logs", web_server_handle_api_logs);
    web_server_add_route(server, "GET", "/api/plugins", web_server_handle_api_plugins);
    web_server_add_route(server, "GET", "/api/version", web_server_handle_api_version);
    web_server_add_route(server, "GET", "/api/check-update", web_server_handle_api_check_update);
    web_server_add_route(server, "GET", "/api/update-status", web_server_handle_api_update_status);
    web_server_add_route(server, "POST", "/api/update", web_server_handle_api_update);
    web_server_add_route(server, "GET", "/api/experiences", web_server_handle_api_experiences);
    web_server_add_route(server, "POST", "/api/experience-control", web_server_handle_api_experience_control);
    web_server_add_route(server, "GET", "/", web_server_handle_dashboard);
}

/* Default handlers */
struct http_response web_server_handle_not_found(const struct http_request* request) {
    struct http_response response;
    const char* html;
    (void)request; /* Suppress unused parameter warning */
    memset(&response, 0, sizeof(response));
    response.status_code = 404;
    web_server_strcpy_safe(response.content_type, "text/html", sizeof(response.content_type));

    html =
        "<!DOCTYPE html>\n"
        "<html>\n"
        "<head>\n"
        "    <title>404 - Not Found</title>\n"
        "    <style>\n"
        "        body { font-family: Arial, sans-serif; text-align: center; margin-top: 50px; }\n"
        "        h1 { color: #e74c3c; }\n"
        "    </style>\n"
        "</head>\n"
        "<body>\n"
        "    <h1>404 - Page Not Found</h1>\n"
        "    <p>The requested resource was not found.</p>\n"
        "    <a href=\"/\">Return to Dashboard</a>\n"
        "</body>\n"
        "</html>\n";
    
    web_server_strcpy_safe(response.body, html, sizeof(response.body));
    return response;
}

struct http_response web_server_handle_api_status(const struct http_request* request) {
    struct http_response response;
    time_t now;
    time_t start_time;
    time_t uptime_seconds;
    char json[512];
    (void)request; /* Suppress unused parameter warning */
    memset(&response, 0, sizeof(response));
    response.status_code = 200;
    web_server_strcpy_safe(response.content_type, "application/json", sizeof(response.content_type));

    /* Calculate actual uptime */
    now = time(NULL);
    start_time = get_daemon_start_time();
    uptime_seconds = now - start_time;

    snprintf(json, sizeof(json),
        "{"
        "\"status\":\"running\","
        "\"uptime\":%ld,"
        "\"version\":\"%s\","
        "\"timestamp\":%ld"
        "}", uptime_seconds, version_get_string(), now);
    
    web_server_strcpy_safe(response.body, json, sizeof(response.body));
    return response;
}

struct http_response web_server_handle_api_metrics(const struct http_request* request) {
    struct http_response response;
    char *json_data;
    (void)request; /* Suppress unused parameter warning */
    memset(&response, 0, sizeof(response));
    response.status_code = 200;
    web_server_strcpy_safe(response.content_type, "application/json", sizeof(response.content_type));

    /* Use C89 metrics API - simplified version */
    json_data = metrics_export_json();
    if (json_data) {
        web_server_strcpy_safe(response.body, json_data, sizeof(response.body));
        free(json_data);
    } else {
        web_server_strcpy_safe(response.body, "{\"error\":\"Failed to export metrics\"}", sizeof(response.body));
    }
    return response;
}

struct http_response web_server_handle_api_health(const struct http_request* request) {
    struct http_response response;
    health_status_t overall_status;
    health_check_t checks[32];
    int checks_count;
    char escaped_overall[32];
    char json[2048];
    char* ptr;
    size_t remaining;
    int written;
    int i;
    int first = 1;
    (void)request; /* Suppress unused parameter warning */
    memset(&response, 0, sizeof(response));
    response.status_code = 200;
    web_server_strcpy_safe(response.content_type, "application/json", sizeof(response.content_type));

    overall_status = health_monitor_get_overall_status();
    checks_count = health_monitor_get_all_checks(checks, 32);

    /* Reflect health in the HTTP status so liveness/readiness probes and load
     * balancers can detect an unhealthy daemon without parsing the body. */
    response.status_code = health_monitor_status_is_serving(overall_status) ? 200 : 503;

    web_server_json_escape(health_monitor_status_to_string(overall_status),
                          escaped_overall, sizeof(escaped_overall));
    ptr = json;
    remaining = sizeof(json);

    written = snprintf(ptr, remaining, "{\"overall_status\":\"%s\",\"checks\":{",
                          escaped_overall);
    if (written > 0 && (size_t)written < remaining) {
        ptr += written;
        remaining -= written;
    }

    for (i = 0; i < checks_count && remaining > 200; i++) {
        char escaped_name[64];
        char escaped_status[32];
        char escaped_message[256];
        web_server_json_escape(checks[i].name, escaped_name, sizeof(escaped_name));
        web_server_json_escape(health_monitor_status_to_string(checks[i].last_status),
                              escaped_status, sizeof(escaped_status));
        web_server_json_escape(checks[i].last_message, escaped_message, sizeof(escaped_message));
        if (!first) {
            written = snprintf(ptr, remaining, ",");
            if (written > 0 && (size_t)written < remaining) {
                ptr += written;
                remaining -= written;
            }
        }
        written = snprintf(ptr, remaining,
            "\"%s\":{\"status\":\"%s\",\"message\":\"%s\",\"last_check\":%ld}",
            escaped_name, escaped_status, escaped_message, checks[i].last_check_time);
        if (written > 0 && (size_t)written < remaining) {
            ptr += written;
            remaining -= written;
        }
        first = 0;
    }
    
    written = snprintf(ptr, remaining, "}}");
    if (written > 0 && (size_t)written < remaining) {
        ptr += written;
        remaining -= written;
    }
    
    web_server_strcpy_safe(response.body, json, sizeof(response.body));
    return response;
}
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
